jaycee1980/zxspec-greyplus2-sram/pictures/fitted.jpg

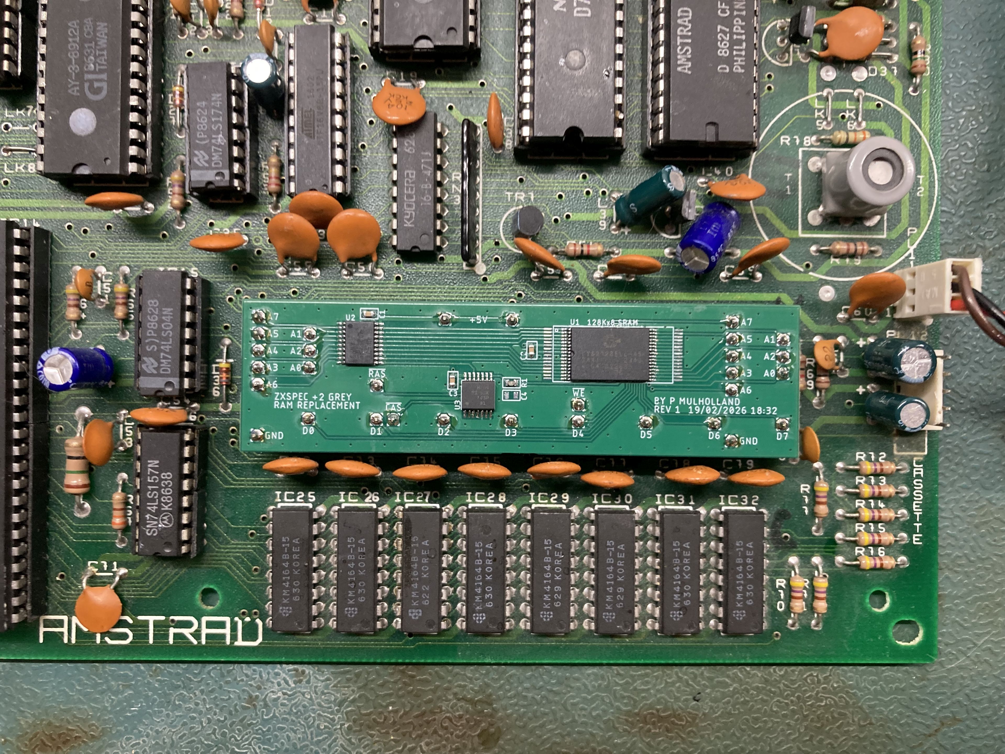
pictures/fitted.jpg
